Bully85/Sovol-SV04-Klipper/config/SV04-with-display/adxl345.cfg

[mcu rpi]
serial: /tmp/klipper_host_mcu

[adxl345]
cs_pin: rpi:None

[resonance_tester]
accel_chip: adxl345
probe_points:
    150.5,160,100

#[input_shaper]
#shaper_freq_x: 82.0
#shaper_freq_y: 82.0
#shaper_freq_dc: 82.0
#shaper_type_x: mzv
#shaper_type_y: ei
#shaper_type_dc: mzv

###inputshaper macros:
 
[gcode_macro ADXL_X]
description: test resonances in x direction / of the hotend
gcode:
  M118 DO NOT TOUCH THE PRINTER UNTIL DONE!!!
  home_check		#or g28 if you dont have a macro to check if you orinter is homed
  SHAPER_CALIBRATE AXIS=x
  RUN_SHELL_COMMAND CMD=adxl_x
  M118 Test done
  SAVE_CONFIG
 
[gcode_macro ADXL_Y]
description: test resonances in y direction / of the heated bed
gcode:
  M118 DO NOT TOUCH THE PRINTER UNTIL DONE!!!
  home_check  		#or g28
  SHAPER_CALIBRATE AXIS=y
  RUN_SHELL_COMMAND CMD=adxl_y
  M118 Test done
  SAVE_CONFIG
 
#########################################################################################################################
###shell commands:
 
### create a file named: adxl_x.sh
#~/klipper/scripts/calibrate_shaper.py /tmp/calibration_data_x_*.csv -o ~/klipper_config/shaper_calibrate_x.png

### create a file named: adxl_dc.sh
#~/klipper/scripts/calibrate_shaper.py /tmp/calibration_data_dc_*.csv -o ~/klipper_config/shaper_calibrate_dc.png
 
### create a file named: adxl_y.sh
#~/klipper/scripts/calibrate_shaper.py /tmp/calibration_data_y_*.csv -o ~/klipper_config/shaper_calibrate_y.png
 
#########################################################################################################################
###shell commands to run in klipper:
 
[gcode_shell_command adxl_x]
command: sh /home/pi/printer_data/config/macro/shell_commands/adxl_x.sh	
# edit: ´klipper_config/macro/shell_commands/´ to where your .sh file lays 
timeout: 60.
verbose: True
 
[gcode_shell_command adxl_y]
command: sh /home/pi/printer_data/config/macro/shell_commands/adxl_y.sh		
# edit: ´klipper_config/macro/shell_commands/´ to where your .sh file lays
timeout: 60.
verbose: True
